simonfojtu/air_conditioner_controller/esp8266_ir_transmitter/firmware/user/cgi.h

#ifndef CGI_H
#define CGI_H

#include "httpd.h"

int cgiAC(HttpdConnData *connData);
int tplAC(HttpdConnData *connData, char *token, void **arg);
int tplCounter(HttpdConnData *connData, char *token, void **arg);

#endif
