simonfojtu/air_conditioner_controller/esp8266_ir_transmitter/firmware/user/io.c

/*
 * ----------------------------------------------------------------------------
 * "THE BEER-WARE LICENSE" (Revision 42):
 * Jeroen Domburg <jeroen@spritesmods.com> wrote this file. As long as you retain 
 * this notice you can do whatever you want with this stuff. If we meet some day, 
 * and you think this stuff is worth it, you can buy me a beer in return. 
 * ----------------------------------------------------------------------------
 */


#include <esp8266.h>

#define LEDGPIO 2
#define BTNGPIO 0

static ETSTimer resetBtntimer;

static void ICACHE_FLASH_ATTR resetBtnTimerCb(void *arg) {
	static int resetCnt=0;
	if (!GPIO_INPUT_GET(BTNGPIO)) {
		resetCnt++;
	} else {
		if (resetCnt>=6) { //3 sec pressed
			wifi_station_disconnect();
			wifi_set_opmode(0x3); //reset to AP+STA mode
			os_printf("Reset to AP mode. Restarting system...\n");
			system_restart();
		}
		resetCnt=0;
	}
}

void ioInit() {
	PIN_FUNC_SELECT(PERIPHS_IO_MUX_GPIO2_U, FUNC_GPIO2);
	PIN_FUNC_SELECT(PERIPHS_IO_MUX_GPIO0_U, FUNC_GPIO0);
//	gpio_output_set(0, 0, (1<<LEDGPIO), (1<<BTNGPIO));
	os_timer_disarm(&resetBtntimer);
	os_timer_setfn(&resetBtntimer, resetBtnTimerCb, NULL);
	os_timer_arm(&resetBtntimer, 500, 1);
}
